yakla/minecraft-lectrern-hackpad/laser dxf files/fast model - top plate bottom.dxf

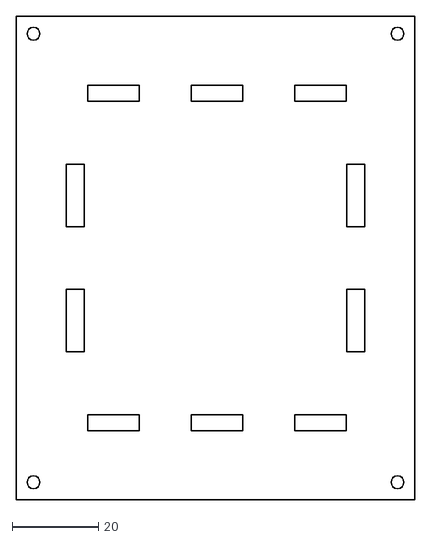
[picture p15: CAD file, 2026-03-28]
laser dxf files/fast model - top plate bottom.dxf
92.4 x 112.0
