yakla/minecraft-lectrern-hackpad/cad/parts/fast model - left side pannel.step

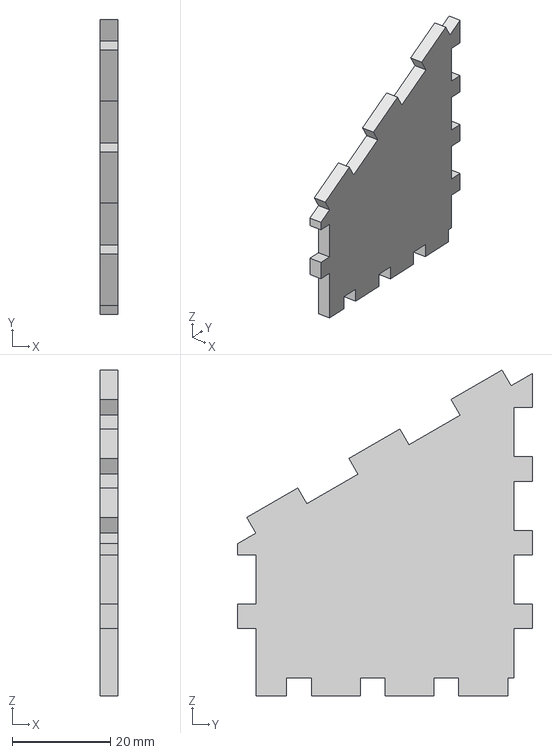
[picture p16: CAD file, 2026-03-26]
cad/parts/fast model - left side pannel.step
3.70 x 60.0 x 66.3 mm
