yakla/minecraft-lectrern-hackpad/laser dxf files/fast model - base top.dxf

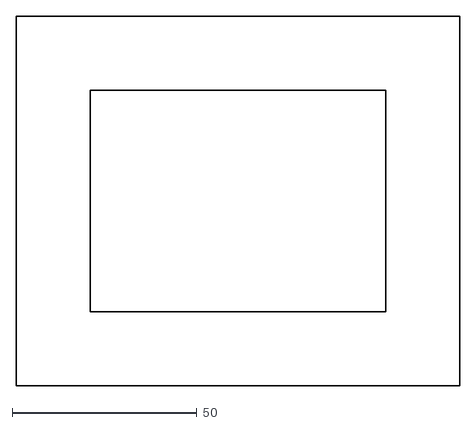
[picture p17: CAD file, 2026-03-28]
laser dxf files/fast model - base top.dxf
120.0 x 100.0
