yakla/minecraft-lectrern-hackpad/cad/parts/fast model - front pannel.step

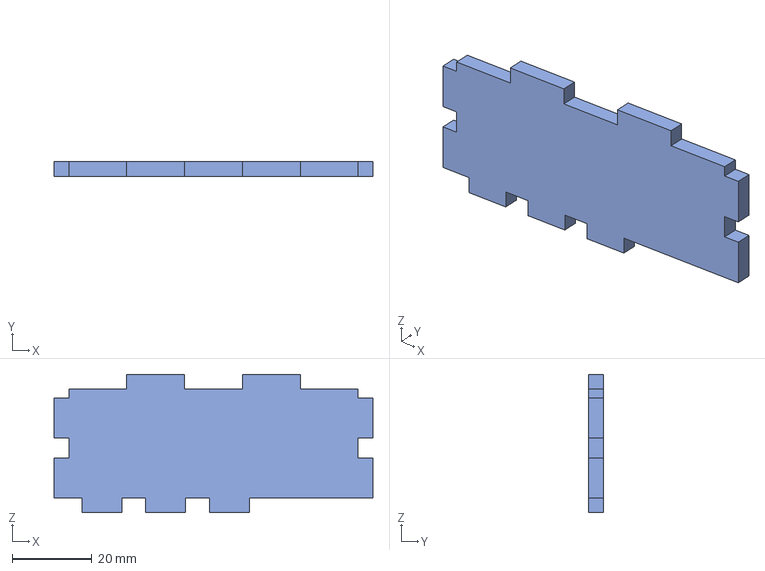
[picture p18: CAD file, 2026-03-26]
cad/parts/fast model - front pannel.step
80.0 x 3.70 x 34.7 mm
